gzip/eagle-usb-gamepad/firmware/4nes4snes-1.4.2-bitkit/gamepad.h

#ifndef _gamepad_h__
#define _gamepad_h__

typedef struct {
	// size of reports built by buildReport
	char num_reports;

	int reportDescriptorSize;
	void *reportDescriptor; // must be in flash

	int deviceDescriptorSize; // if 0, use default
	void *deviceDescriptor; // must be in flash
	
	void (*init)(void);
	void (*update)(void);

	char (*changed)(unsigned char id);
	/**
	 * \param id Controller id (starting at 1 to match report IDs)
	 * \return The number of bytes written to buf.
	 * */
	char (*buildReport)(unsigned char *buf, char id);
} Gamepad;

#endif // _gamepad_h__
