gzip/eagle-usb-gamepad/firmware/nes_snes_db9_usb-1.9-bitkit/usbdrv/usbdrvasm.asm

/* Name: usbdrvasm.asm
 * Project: AVR USB driver
 * Author: Christian Starkjohann
 * Creation Date: 2006-03-01
 * Tabsize: 4
 * Copyright: (c) 2006 by OBJECTIVE DEVELOPMENT Software GmbH
 * License: GNU GPL v2 (see License.txt) or proprietary (CommercialLicense.txt)
 * This Revision: $Id: usbdrvasm.asm,v 1.2 2007/11/10 23:56:24 raph Exp $
 */

/*
General Description:
The IAR compiler/assembler system prefers assembler files with file extension
".asm". We simply provide this file as an alias for usbdrvasm.S.

Thanks to Oleg Semyonov for his help with the IAR tools port!
*/

#include "usbdrvasm.S"

end
